heinervdm/ESP8266-Temperatursensor/user/onewire.c

/* 
Access Dallas 1-Wire Devices with ATMEL AVRs
Author of the initial code: Peter Dannegger (danni(at)specs.de)
modified by Martin Thomas (mthomas(at)rhrk.uni-kl.de)
ported to esp8266 by Thomas Zimmermann (bugs(at)vdm-design.de)
 9/2004 - use of delay.h, optional bus configuration at runtime
10/2009 - additional delay in ow_bit_io for recovery
 5/2010 - timing modifcations, additonal config-values and comments,
          use of atomic.h macros, internal_t pull-up support
 7/2010 - added method to skip recovery time after last bit transfered
          via ow_command_skip_last_recovery
 7/2015 - ported to ESP8266
*/
#include "ets_sys.h"
#include "espmissingincludes.h"
#include "c_types.h"
#include "osapi.h"
#include "os_type.h"
#include "user_interface.h"
#include "onewire.h"
#include "gpio.h"

#define OW_GET_IN()   ( GPIO_INPUT_GET(OW_PIN) )
#define OW_OUT_LOW()  ( GPIO_OUTPUT_SET(OW_PIN,0) )
#define OW_OUT_HIGH() ( GPIO_OUTPUT_SET(OW_PIN,1) )
#define OW_DIR_IN()   ( GPIO_DIS_OUTPUT(OW_PIN) )

uint8_t ICACHE_FLASH_ATTR ow_input_pin_state() 
{
	return OW_GET_IN();
}

void ICACHE_FLASH_ATTR ow_parasite_enable(void) 
{
	OW_OUT_HIGH();
}

void ICACHE_FLASH_ATTR ow_parasite_disable(void) 
{
	OW_DIR_IN();
}


uint8_t ICACHE_FLASH_ATTR ow_reset(void) 
{
	uint8_t err;
	
	OW_OUT_LOW();            // pull OW-Pin low for 480us
	os_delay_us(480);

	// set Pin as input - wait for clients to pull low
	OW_DIR_IN(); // input
	
	os_delay_us(64);       // was 66
	err = OW_GET_IN();   // no presence detect
	                     // if err!=0: nobody pulled to low, still high

	// after a delay the clients should release the line
	// and input-pin gets back to high by pull-up-resistor
	os_delay_us(480 - 64);       // was 480-66
	if( OW_GET_IN() == 0 ) {
		err = 1;             // short circuit, expected low but got high
	}
	
	return err;
}


/* Timing issue when using runtime-bus-selection (!OW_ONE_BUS):
   The master should sample at the end of the 15-slot after initiating
   the read-time-slot. The variable bus-settings need more
   cycles than the constant ones so the delays had to be shortened 
   to achive a 15uS overall delay 
   Setting/clearing a bit in I/O Register needs 1 cyle in OW_ONE_BUS
   but around 14 cyles in configureable bus (us-Delay is 4 cyles per uS) */
static uint8_t ICACHE_FLASH_ATTR ow_bit_io_intern_t( uint8_t b, uint8_t with_parasite_enable ) 
{
	OW_OUT_LOW();
	os_delay_us(2);    // T_INT > 1usec accoding to timing-diagramm
	if ( b ) {
		OW_DIR_IN(); // to write "1" release bus, resistor pulls high
	}

	// "Output data from the DS18B20 is valid for 15usec after the falling
	// edge that initiated the read time slot. Therefore, the master must 
	// release the bus and then sample the bus state within 15ussec from 
	// the start of the slot."
	os_delay_us(15-2);
	
	if( OW_GET_IN() == 0 ) {
		b = 0;  // sample at end of read-timeslot
	}

	os_delay_us(60-15-2);
	OW_DIR_IN();

	if ( with_parasite_enable ) {
		ow_parasite_enable();
	}

	os_delay_us(OW_RECOVERY_TIME); // may be increased for longer wires

	return b;
}

uint8_t ICACHE_FLASH_ATTR ow_bit_io( uint8_t b ) 
{
	return ow_bit_io_intern_t( b & 1, 0 );
}

uint8_t ICACHE_FLASH_ATTR ow_byte_wr( uint8_t b ) 
{
	uint8_t i = 8, j;
	
	do {
		j = ow_bit_io( b & 1 );
		b >>= 1;
		if( j ) {
			b |= 0x80;
		}
	} while( --i );
	
	return b;
}

uint8_t ICACHE_FLASH_ATTR ow_byte_wr_with_parasite_enable( uint8_t b ) 
{
	uint8_t i = 8, j;
	
	do {
		if ( i != 1 ) {
			j = ow_bit_io_intern_t( b & 1, 0 );
		} else {
			j = ow_bit_io_intern_t( b & 1, 1 );
		}
		b >>= 1;
		if( j ) {
			b |= 0x80;
		}
	} while( --i );
	
	return b;
}


uint8_t ICACHE_FLASH_ATTR ow_byte_rd( void ) 
{
	// read by sending only "1"s, so bus gets released
	// after the init low-pulse in every slot
	return ow_byte_wr( 0xFF ); 
}


uint8_t ICACHE_FLASH_ATTR ow_rom_search( uint8_t diff, uint8_t *id ) 
{
	uint8_t i, j, next_diff;
	uint8_t b;
	
	if( ow_reset() ) {
		return OW_PRESENCE_ERR;         // error, no device found <--- early exit!
	}
	
	ow_byte_wr( OW_SEARCH_ROM );        // ROM search command
	next_diff = OW_LAST_DEVICE;         // unchanged on last device
	
	i = OW_ROMCODE_SIZE * 8;            // 8 bytes
	
	do {
		j = 8;                          // 8 bits
		do {
			b = ow_bit_io( 1 );         // read bit
			if( ow_bit_io( 1 ) ) {      // read complement bit
				if( b ) {               // 0b11
					return OW_DATA_ERR; // data error <--- early exit!
				}
			}
			else {
				if( !b ) {              // 0b00 = 2 devices
					if( diff > i || ((*id & 1) && diff != i) ) {
						b = 1;          // now 1
						next_diff = i;  // next pass 0
					}
				}
			}
			ow_bit_io( b );             // write bit
			*id >>= 1;
			if( b ) {
				*id |= 0x80;            // store bit
			}
			
			i--;
			
		} while( --j );
		
		id++;                           // next byte
	
	} while( i );
	
	return next_diff;                   // to continue search
}


static void ICACHE_FLASH_ATTR ow_command_intern_t( uint8_t command, uint8_t *id, uint8_t with_parasite_enable ) 
{
	uint8_t i;

	ow_reset();

	if( id ) {
		ow_byte_wr( OW_MATCH_ROM );     // to a single device
		i = OW_ROMCODE_SIZE;
		do {
			ow_byte_wr( *id );
			id++;
		} while( --i );
	} 
	else {
		ow_byte_wr( OW_SKIP_ROM );      // to all devices
	}
	
	if ( with_parasite_enable  ) {
		ow_byte_wr_with_parasite_enable( command );
	} else {
		ow_byte_wr( command );
	}
}

void ICACHE_FLASH_ATTR ow_command( uint8_t command, uint8_t *id ) 
{
	ow_command_intern_t( command, id, 0);
}

void ICACHE_FLASH_ATTR ow_command_with_parasite_enable( uint8_t command, uint8_t *id ) 
{
	ow_command_intern_t( command, id, 1 );
}
